Niels-Clayton/Class-D_Amplifier/docs/images/input_HPF_comparison.png

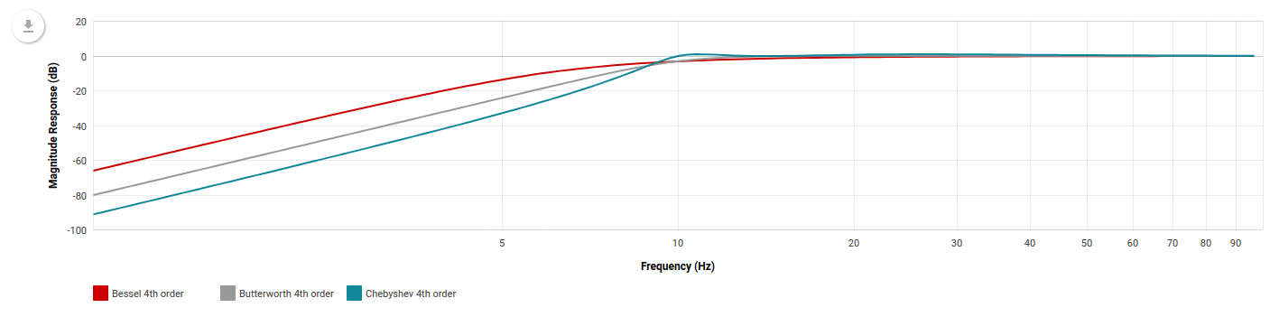
docs/images/input_HPF_comparison.png
