Niels-Clayton/Class-D_Amplifier/docs/images/input_HPF_sim_1.png

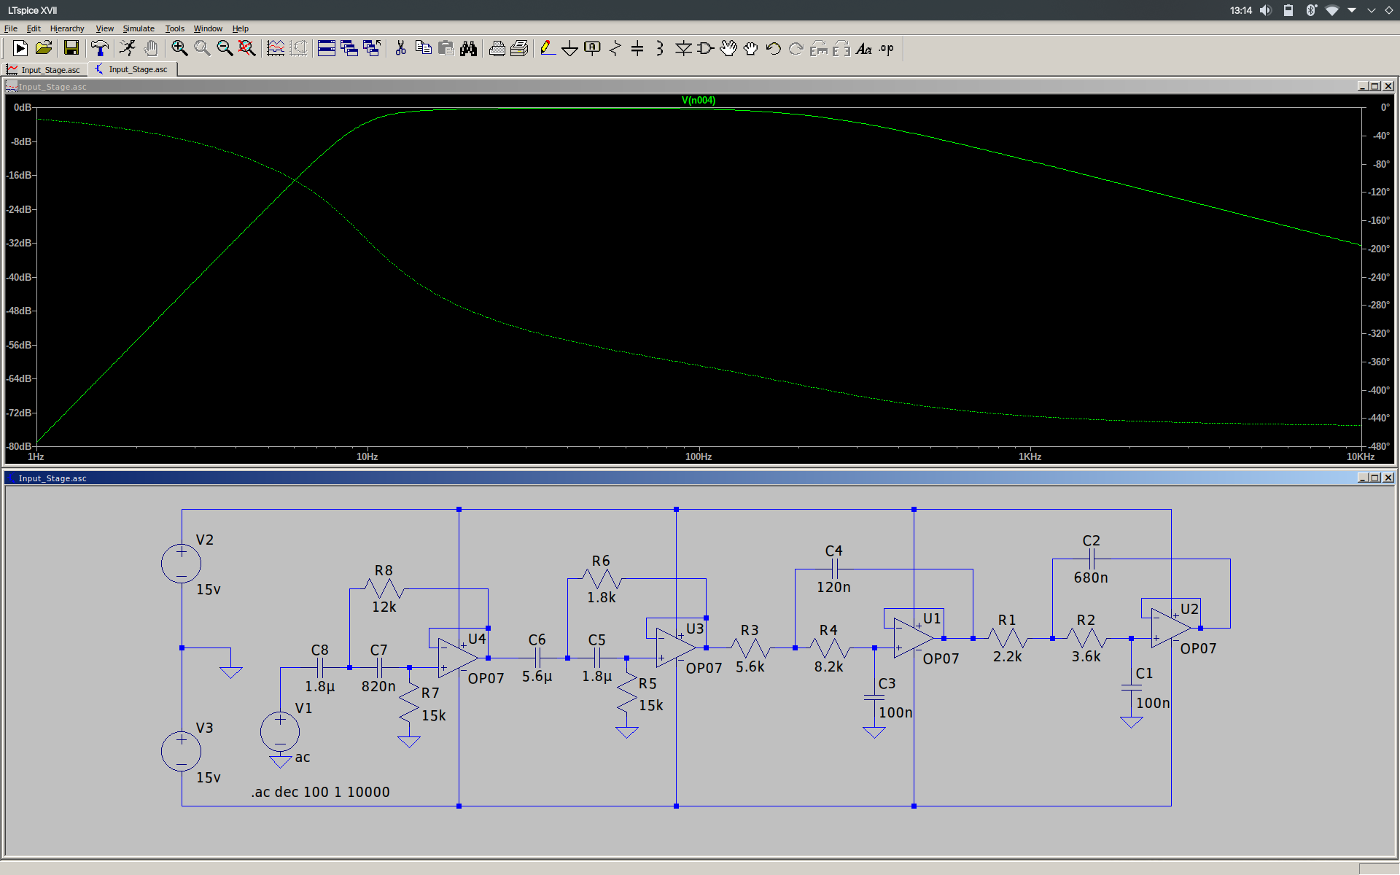
docs/images/input_HPF_sim_1.png
