Niels-Clayton/Class-D_Amplifier/docs/images/input_LPF_comparison.png

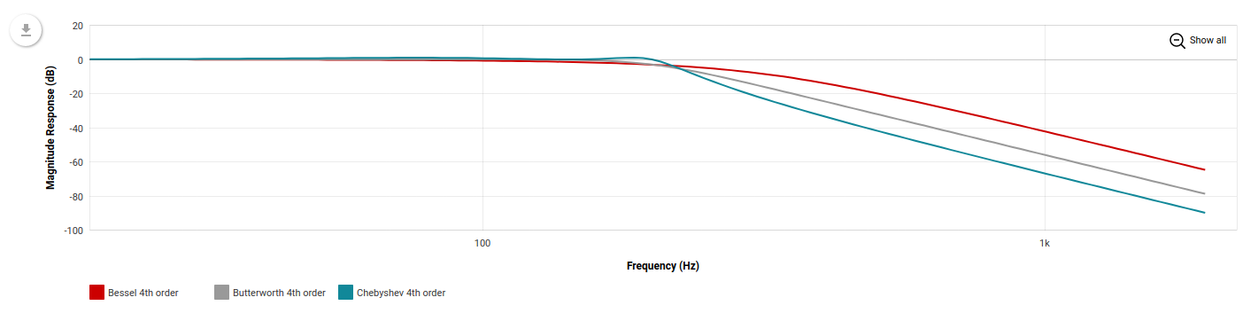
docs/images/input_LPF_comparison.png
