Niels-Clayton/Class-D_Amplifier/docs/images/input_LPF_sim_1.png

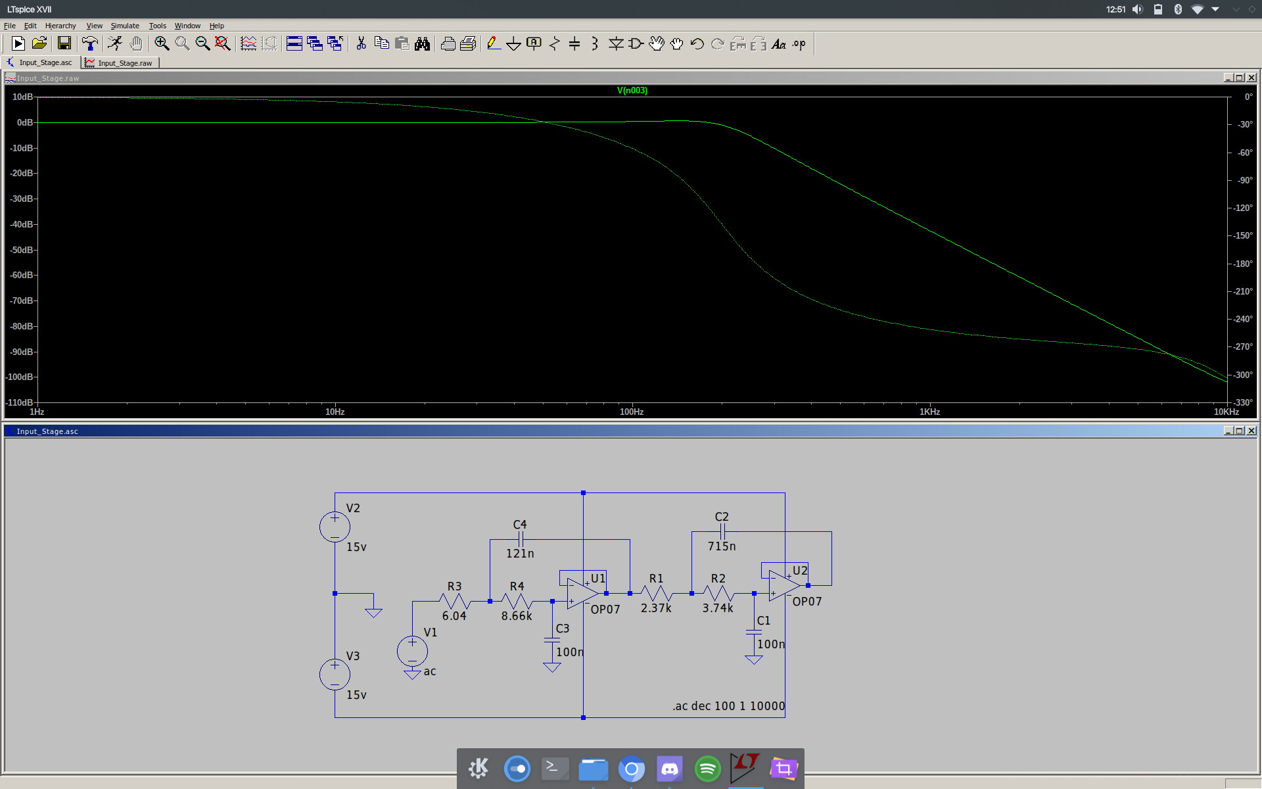
docs/images/input_LPF_sim_1.png
