Niels-Clayton/Class-D_Amplifier/docs/images/input_LPF_sim_2.png

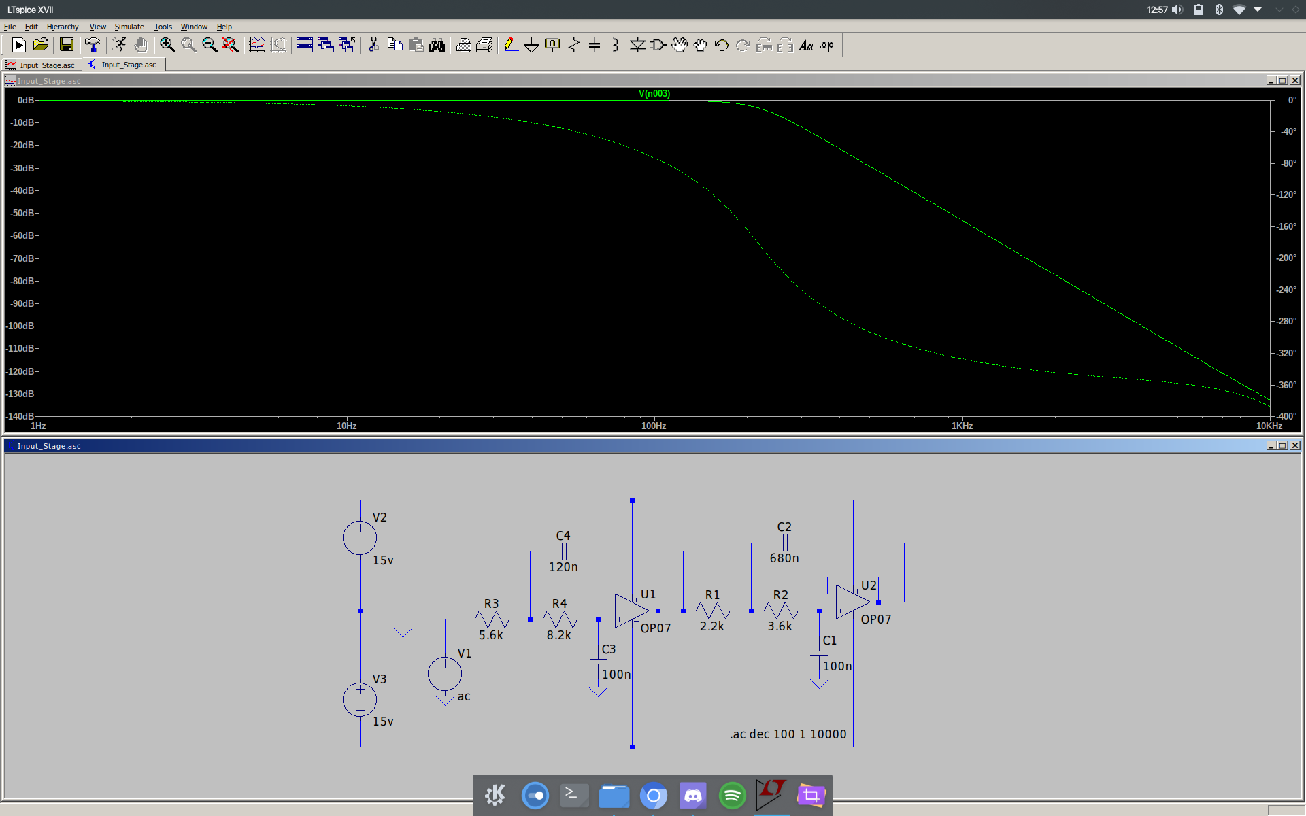
docs/images/input_LPF_sim_2.png
