Niels-Clayton/Class-D_Amplifier/spice_sim/SPWM_Generator/SPWM_Generator.asc

C1: cap; 15n
R1: res; 200
R2: res; 10k
R3: res; 5k
R4: res; 10k
R7: res; 10k
U1: opamp2; TL972
U2: opamp2; TL972
U3: opamp2; LMV393
U4: opamp2; LMV393
V1: voltage; 5
V2: voltage; 2.5
V3: voltage; SINE(2.5 1 500 0)
Named nets: V+, 0, Vref, Triangle, audio
.tran 0 0.0005 0.0001 0.01 startup
.include lib/LMH6658.lib
.include lib/TL972.lib
.include lib/LMV393.MOD
We the output amplitude to be able to go between 1V pk - pk, to 3V pk - pk.
We get 1V pk - pk when R3 = 2k
We get 3V pk - pk when R3 = 6k
 
We want the frequency to go between 30kHz and 100kHz at 2V pk - pk (R3 = 5k Ohm)
we can find frequency roughly with the following equation: f = (1000/R1) * 30,000
We get 30kHz when R1= 1k Ohm
We get 100kHz when R1 = 200 Ohm
