Niels-Clayton/Class-D_Amplifier/spice_sim/Output_Filter/output_filter.asc

C1: cap; 3.3µ
C2: cap; 3.3µ
C3: cap; 16µ
C4: cap; 2.2µ
C5: cap; 2.2µ
C6: cap; 14µ
C7: cap; 1µ
C8: cap; 1µ
C9: cap; 10µ
L1: ind; 270µ
L2: ind; 270µ
L3: ind; 220µ
L4: ind; 220µ
L5: ind; 150µ
L6: ind; 150µ
R1: res; 4
R2: res; 4
R3: res; 4
V1: voltage; ac
V2: voltage; ac
V3: voltage; ac
Named nets: 0
.ac dec 100 1 100k
