Niels-Clayton/Class-D_Amplifier/spice_sim/Input_Stage/Input_Stage.asc

C1: cap; 100µ
C2: cap; 120n
C3: cap; 100n
C4: cap; 100n
C5: cap; 750n
C6: cap; 2.2µ
C7: cap; 1.2µ
R1: res; 100k
R2: res; 10k
R3: res; 4.3k
R4: res; 5.6k
R5: res; 2.4k
R6: res; 1.5k
R7: res; 6.8k
R8: res; 15k
R9: res; 10k
U1: opamp2; LM324
U2: opamp2; LM324
U3: opamp2; LM324
U4: opamp2; LM324
V1: voltage; 5
V2: voltage; 2.5
V4: voltage; ac
Named nets: 0
.ac dec 100 1 1000
.include LM324.MOD
