Niels-Clayton/Class-D_Amplifier/spice_sim/Output_Filter/trans.asc

C1: cap; 1.88µ
C2: cap; 1.88µ
C3: cap; 9.38µ
L1: ind; 150µ
L2: ind; 150µ
R1: res; 4
V1: voltage; ac
Named nets: 0
.ac dec 100 1 100k
